abarach/4tierplanter/images/IMG_3859.JPG

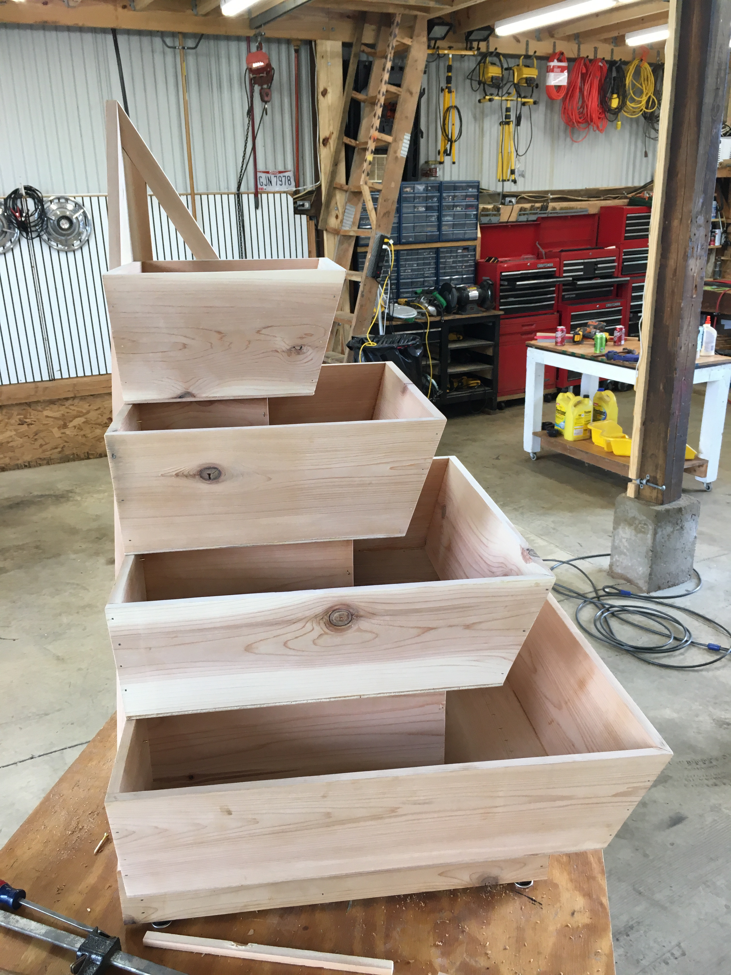
images/IMG_3859.JPG
