abarach/4tierplanter/images/IMG_3863.jpg

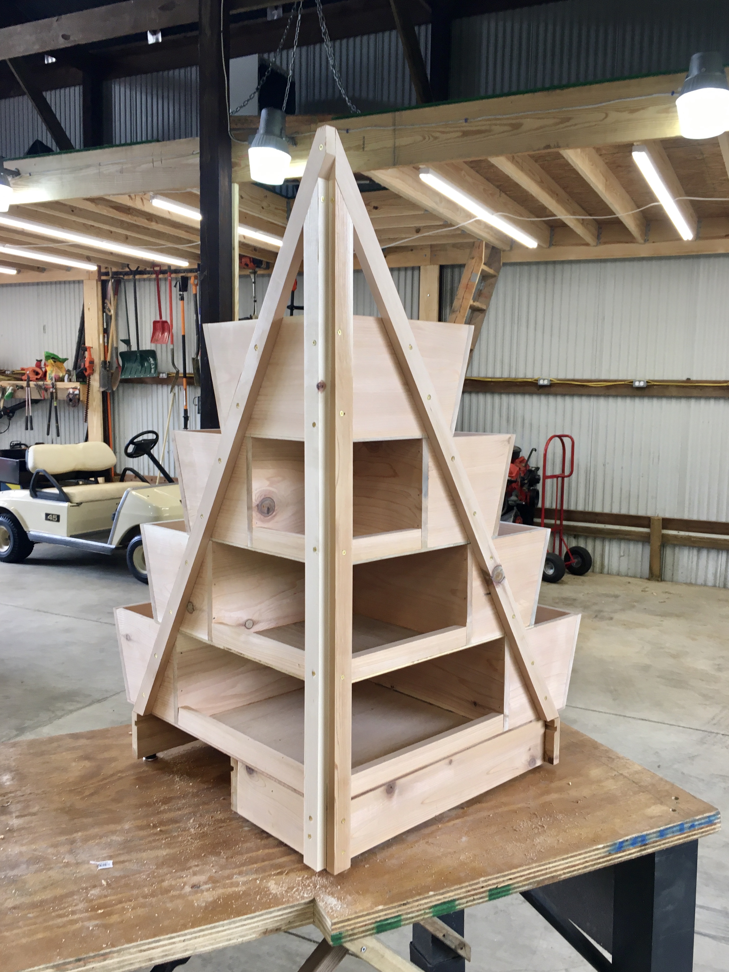
images/IMG_3863.jpg
