abarach/4tierplanter/images/IMG_3864.JPG

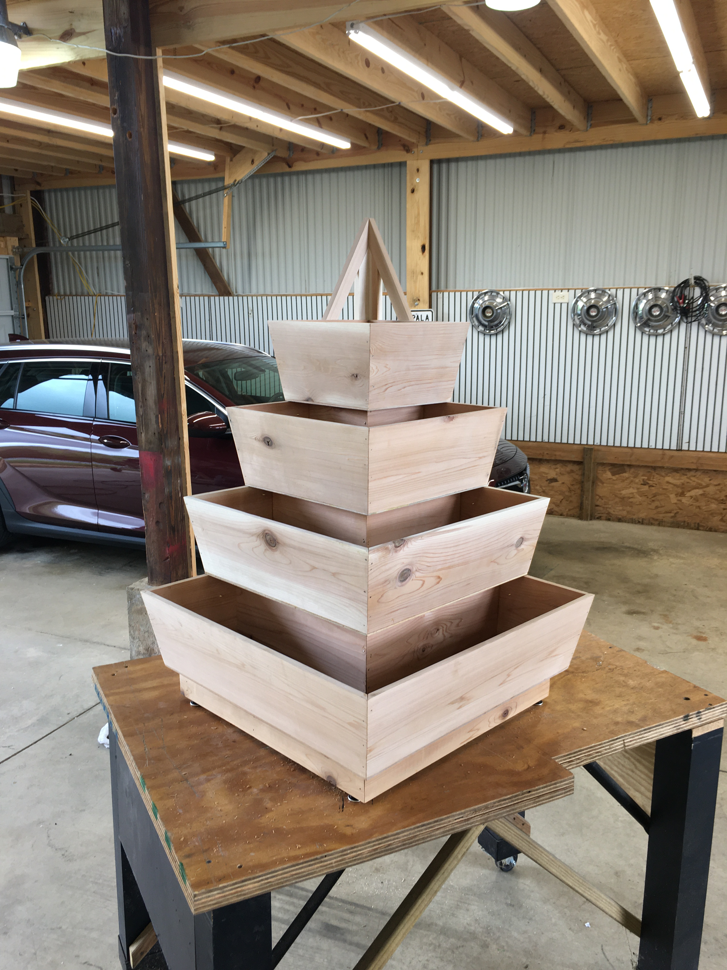
images/IMG_3864.JPG
