abarach/4tierplanter/images/IMG_3903.JPG

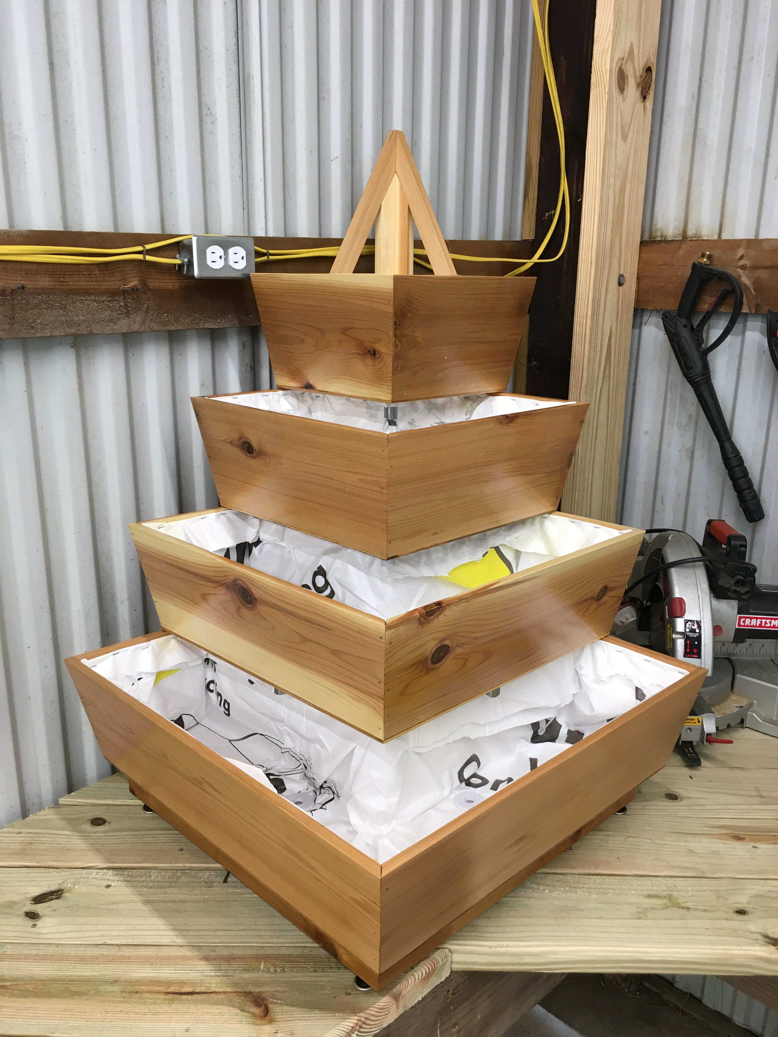
images/IMG_3903.JPG
