abarach/4tierplanter/images/IMG_3906.JPG

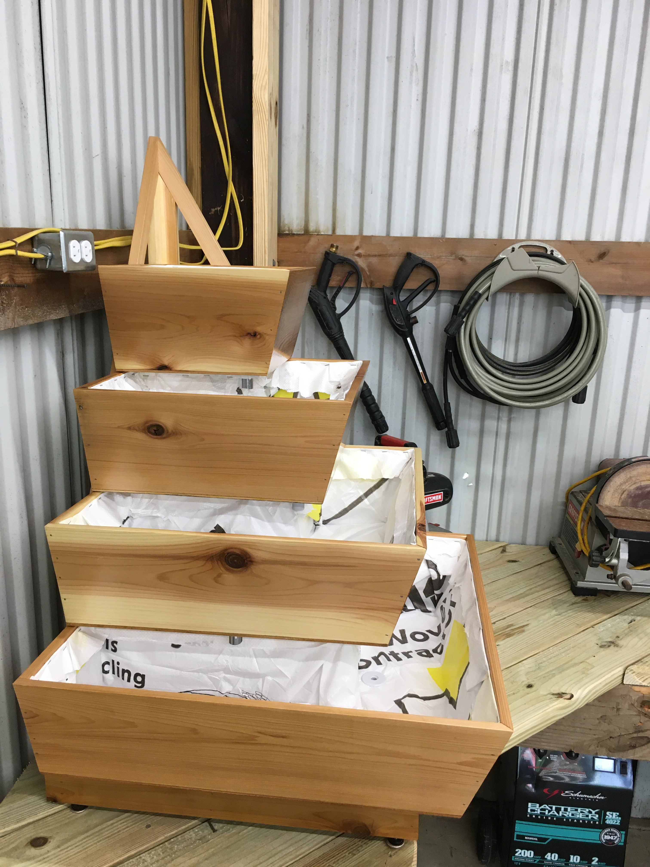
images/IMG_3906.JPG
