abarach/4tierplanter/Planter_Assembly_Files/ShelfEdge_Bottom1.SLDPRT

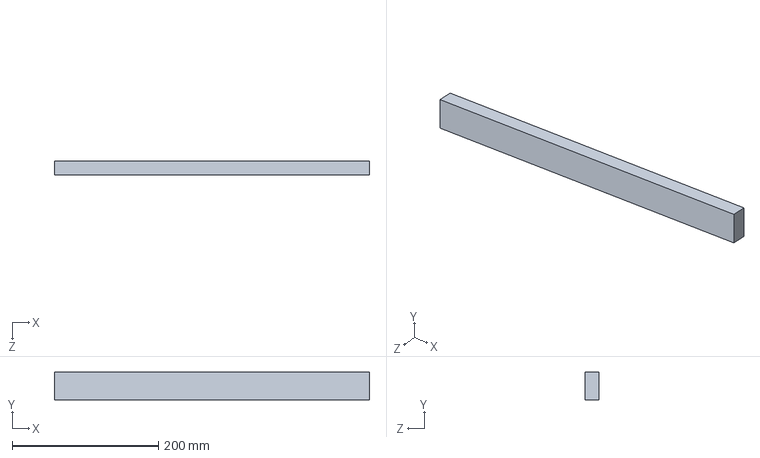
[picture p22: CAD file, 2020-08-23]
Planter_Assembly_Files/ShelfEdge_Bottom1.SLDPRT
431.3 x 38.1 x 19.1 mm
