abarach/4tierplanter/Planter_Assembly_Files/Backpost_1.SLDPRT

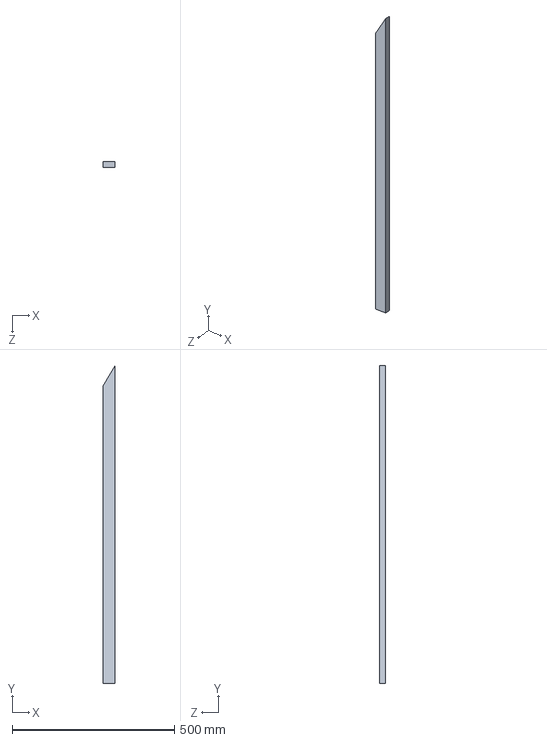
[picture p23: CAD file, 2020-08-23]
Planter_Assembly_Files/Backpost_1.SLDPRT
38.1 x 980.4 x 19.1 mm
