abarach/4tierplanter/Planter_Assembly_Files/Planter_angledWall1-2.SLDPRT

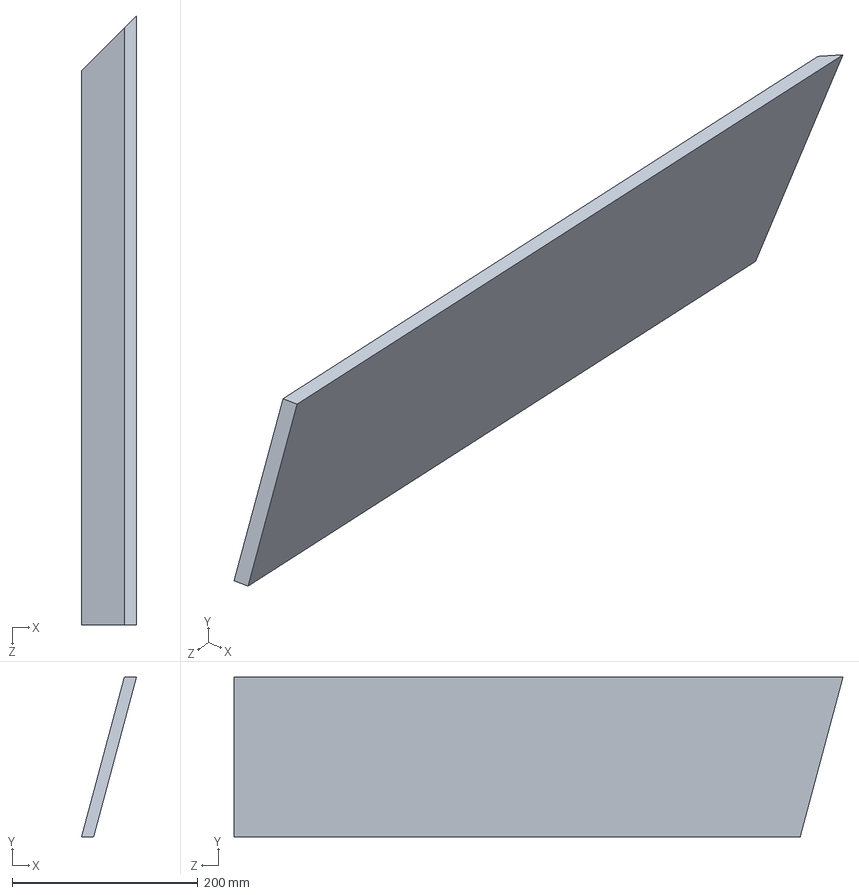
[picture p24: CAD file, 2020-08-23]
Planter_Assembly_Files/Planter_angledWall1-2.SLDPRT
59.2 x 171.7 x 655.6 mm
