abarach/4tierplanter/Planter_Assembly_Files/ShelfEdge_Top1.SLDPRT

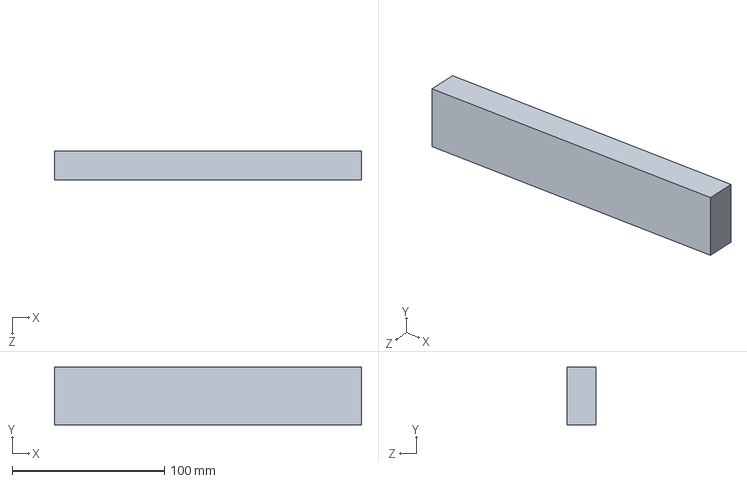
[picture p25: CAD file, 2020-08-23]
Planter_Assembly_Files/ShelfEdge_Top1.SLDPRT
201.8 x 38.1 x 19.1 mm
