abarach/4tierplanter/Planter_Assembly_Files/Planter_backouterSide1.SLDPRT

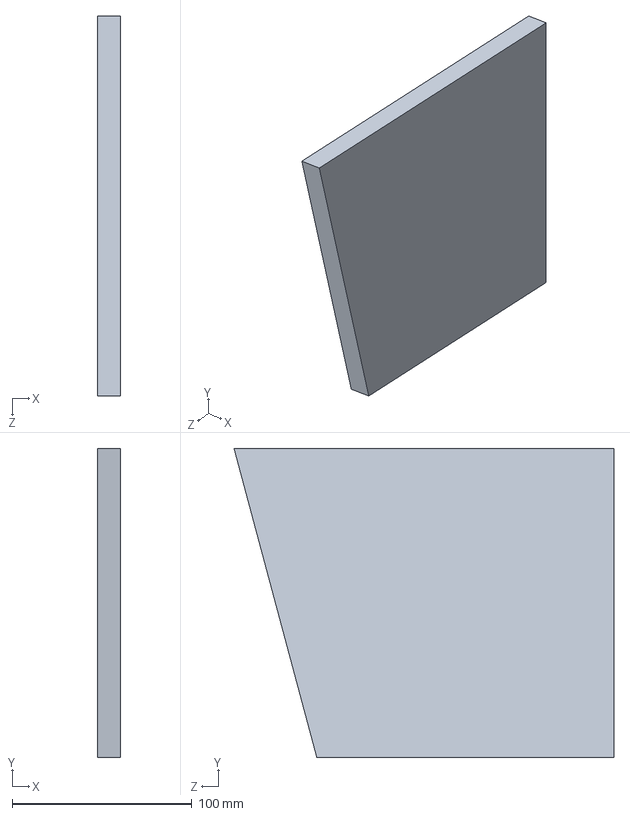
[picture p26: CAD file, 2020-08-23]
Planter_Assembly_Files/Planter_backouterSide1.SLDPRT
12.7 x 171.7 x 211.1 mm
