abarach/4tierplanter/Planter_Assembly_Files/Back_baseboard_1.SLDPRT

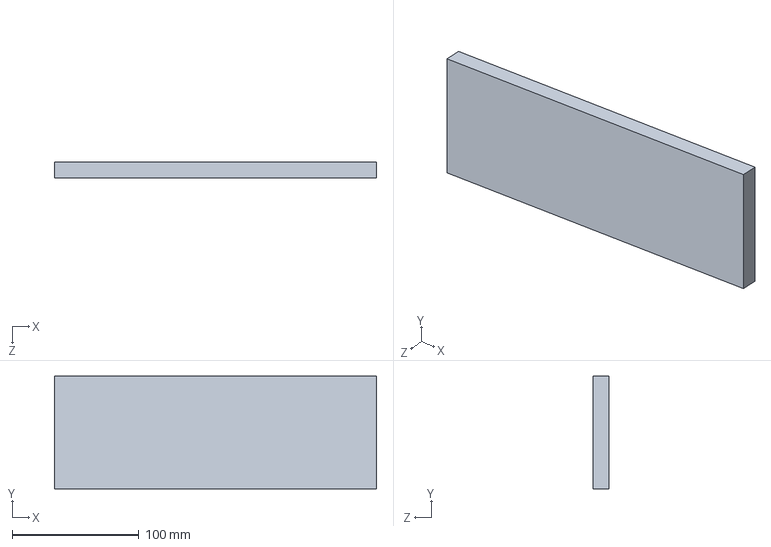
[picture p27: CAD file, 2020-08-23]
Planter_Assembly_Files/Back_baseboard_1.SLDPRT
254.0 x 88.9 x 12.7 mm
