abarach/4tierplanter/Planter_Assembly_Files/Baseboard_1.SLDPRT

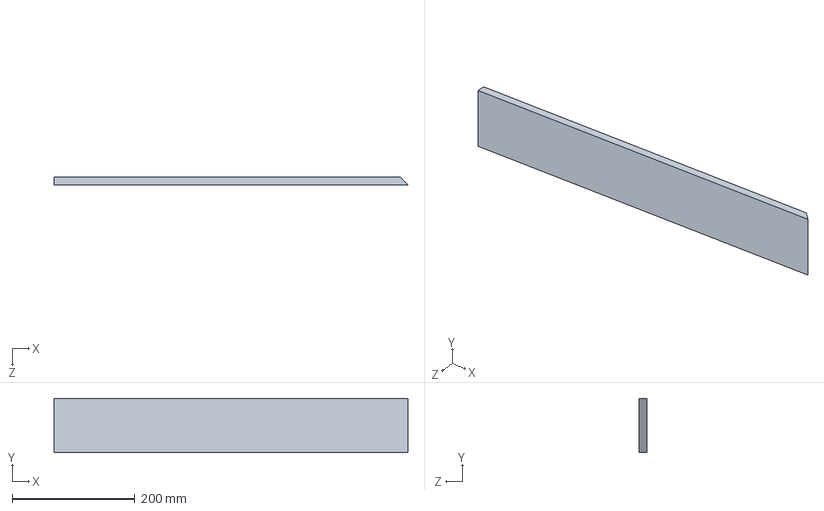
[picture p28: CAD file, 2020-08-23]
Planter_Assembly_Files/Baseboard_1.SLDPRT
577.8 x 88.9 x 12.7 mm
