abarach/4tierplanter/Planter_Assembly_Files/ShelfEdge_Top2.SLDPRT

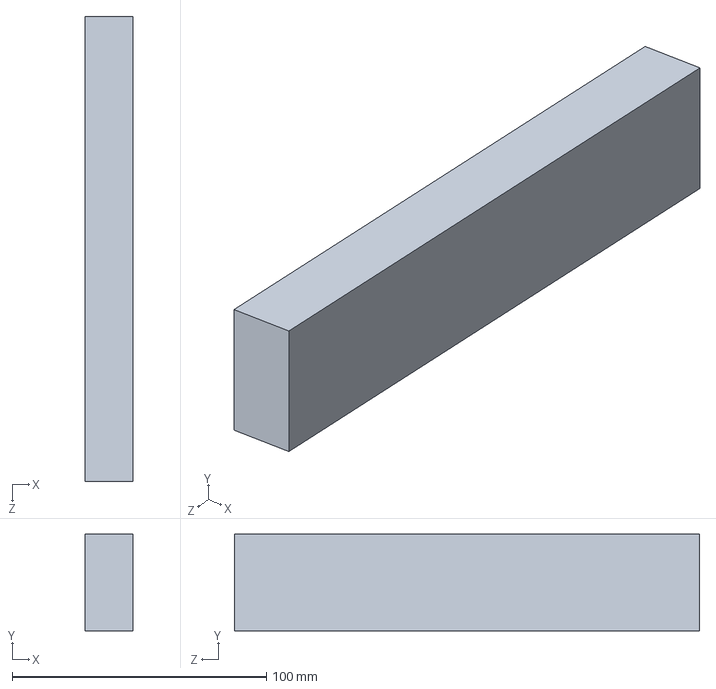
[picture p29: CAD file, 2020-08-23]
Planter_Assembly_Files/ShelfEdge_Top2.SLDPRT
19.1 x 38.1 x 182.8 mm
