abarach/4tierplanter/Planter_Assembly_Files/Planter_floor3.SLDPRT

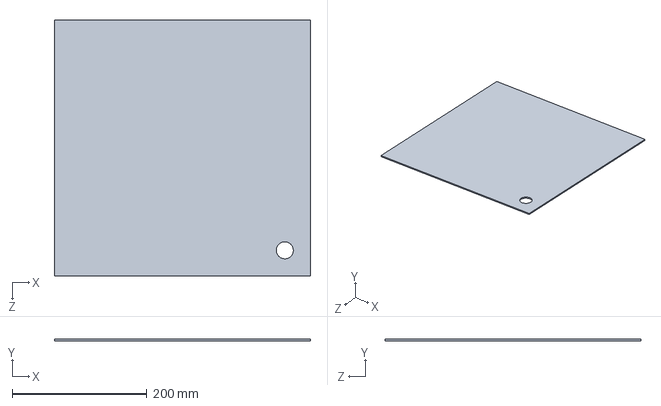
[picture p30: CAD file, 2020-08-23]
Planter_Assembly_Files/Planter_floor3.SLDPRT
380.1 x 2.50 x 380.1 mm
