abarach/4tierplanter/Planter_Assembly_Files/Planter_floor1.SLDPRT

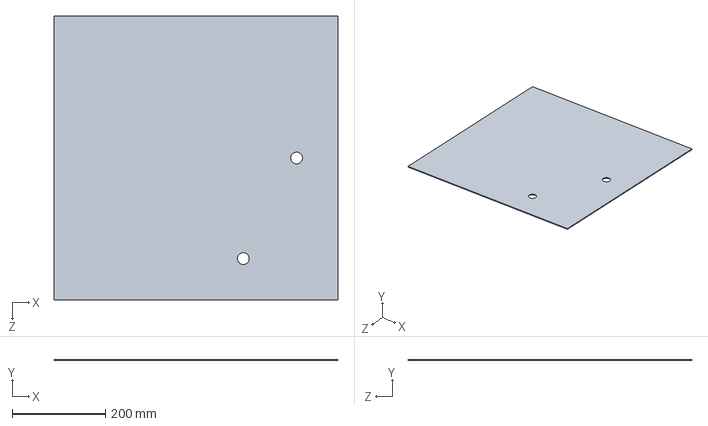
[picture p31: CAD file, 2020-08-23]
Planter_Assembly_Files/Planter_floor1.SLDPRT
609.6 x 2.50 x 609.6 mm
