abarach/4tierplanter/Planter_Assembly_Files/Rails_1.SLDPRT

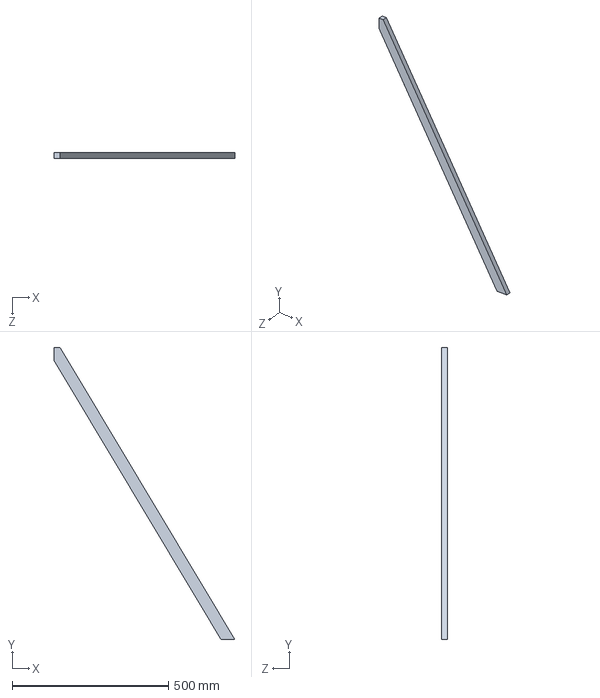
[picture p32: CAD file, 2020-08-23]
Planter_Assembly_Files/Rails_1.SLDPRT
577.9 x 933.7 x 19.1 mm
