abarach/4tierplanter/Planter_Assembly_Files/ShelfEdge_Bottom2.SLDPRT

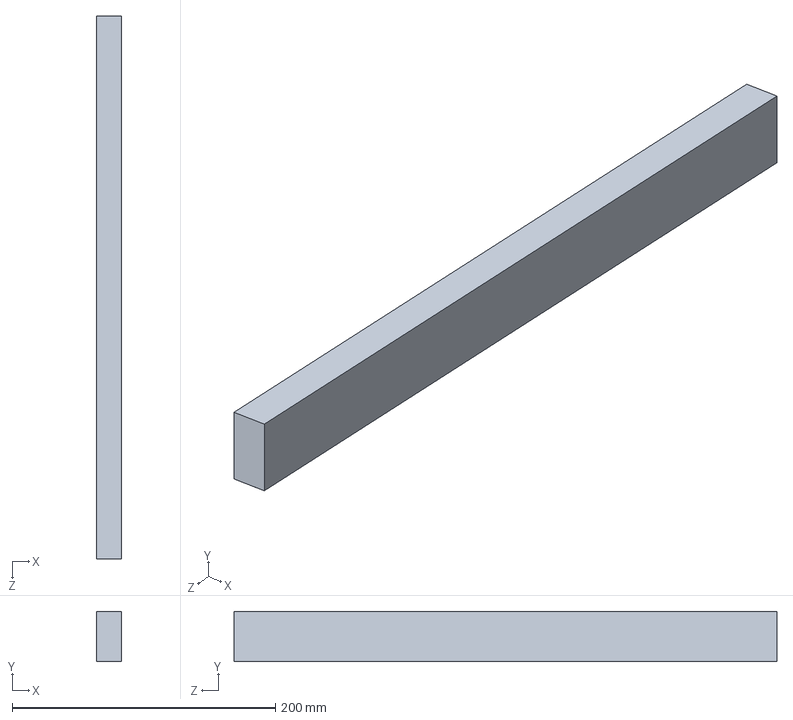
[picture p33: CAD file, 2020-08-23]
Planter_Assembly_Files/ShelfEdge_Bottom2.SLDPRT
19.1 x 38.1 x 412.3 mm
