abarach/4tierplanter/Planter_Assembly_Files/Backpost_2.SLDPRT

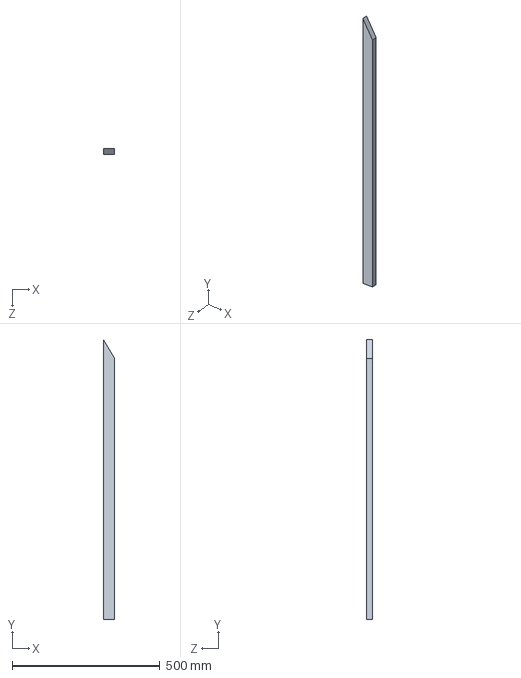
[picture p34: CAD file, 2020-08-23]
Planter_Assembly_Files/Backpost_2.SLDPRT
38.1 x 948.7 x 19.1 mm
