abarach/4tierplanter/Planter_Assembly_Files/Interior_tray_holder.SLDPRT

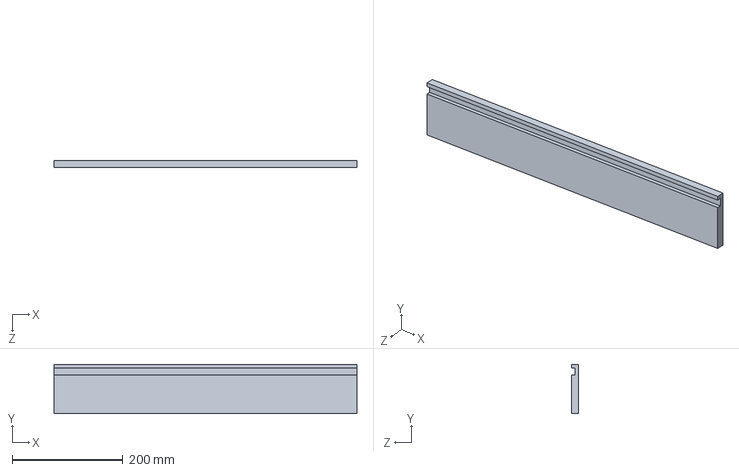
[picture p35: CAD file, 2020-08-23]
Planter_Assembly_Files/Interior_tray_holder.SLDPRT
546.1 x 88.9 x 12.7 mm
